camueller/WeatherStation-Wunderground-GSM/fritzing/WetterstationDaidalos_bb.png

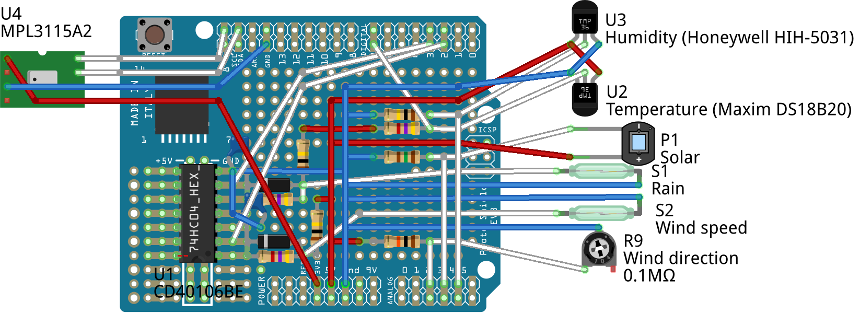
fritzing/WetterstationDaidalos_bb.png
