camueller/WeatherStation-Wunderground-GSM/fritzing/WetterstationDaidalos_schem.png

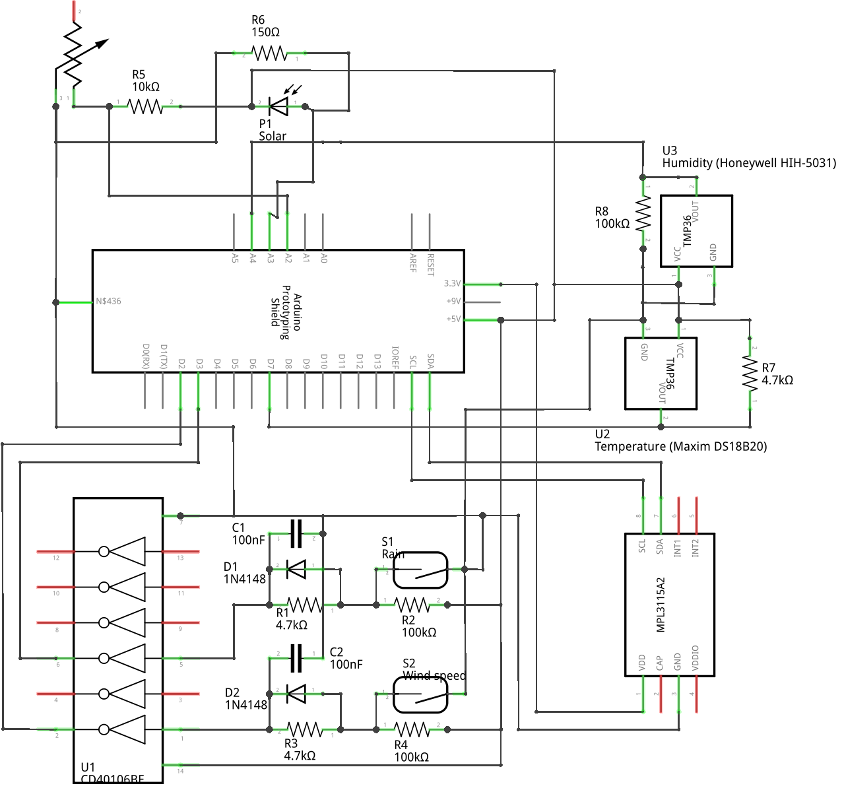
fritzing/WetterstationDaidalos_schem.png
