camueller/WeatherStation-Wunderground-GSM/pics/ArduinoUNO.JPG

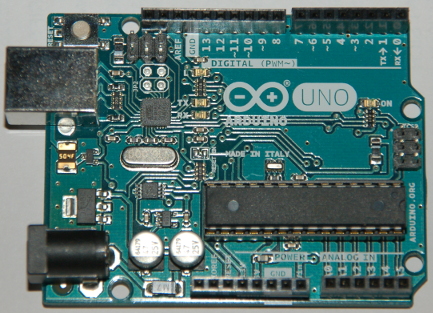
pics/ArduinoUNO.JPG
