camueller/WeatherStation-Wunderground-GSM/pics/Container.JPG

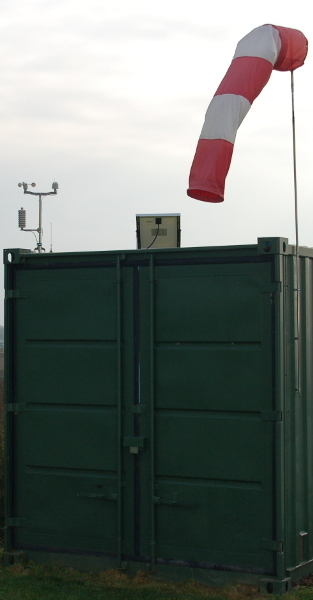
pics/Container.JPG
