camueller/WeatherStation-Wunderground-GSM/pics/EFCom.JPG

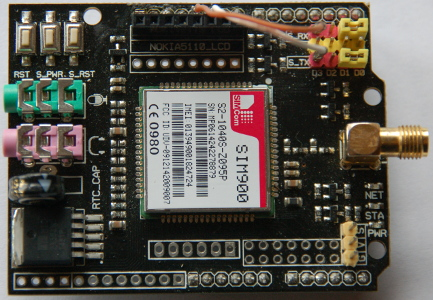
pics/EFCom.JPG
