camueller/WeatherStation-Wunderground-GSM/pics/ProtoShield.JPG

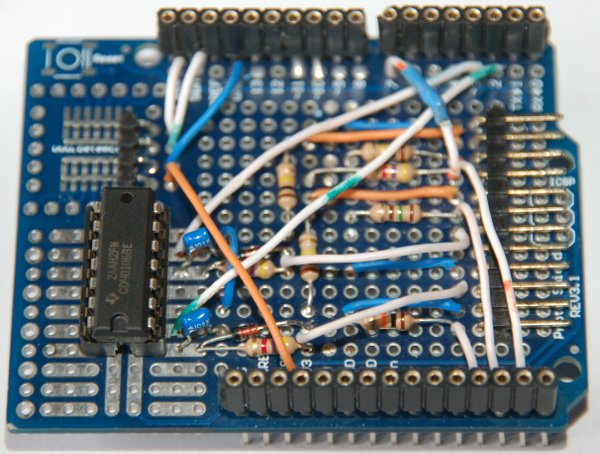
pics/ProtoShield.JPG
