camueller/WeatherStation-Wunderground-GSM/pics/Pyranometer2.JPG

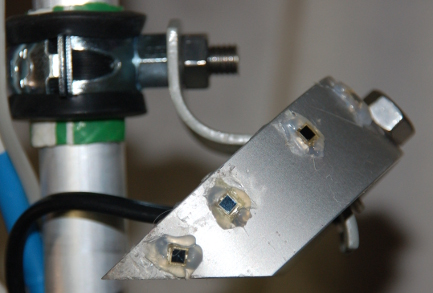
pics/Pyranometer2.JPG
