camueller/WeatherStation-Wunderground-GSM/pics/ShieldStack2.JPG

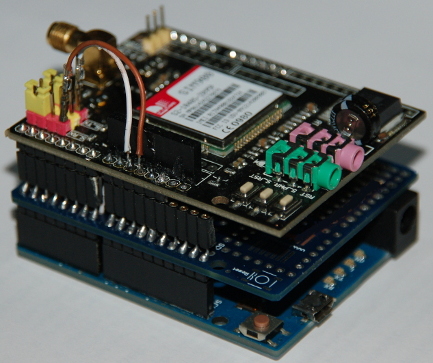
pics/ShieldStack2.JPG
