camueller/WeatherStation-Wunderground-GSM/pics/ShieldStack.JPG

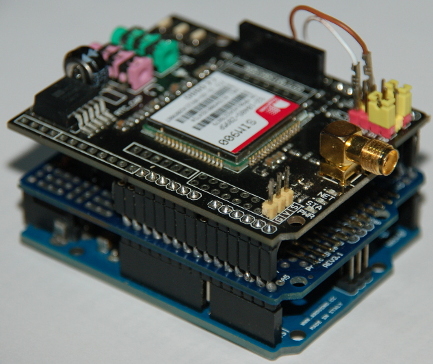
pics/ShieldStack.JPG
