camueller/WeatherStation-Wunderground-GSM/pics/SolarBausatz.png

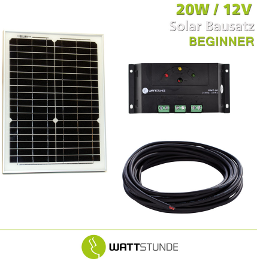
pics/SolarBausatz.png
