camueller/WeatherStation-Wunderground-GSM/pics/sonnenstand_mit_sensoren.gif

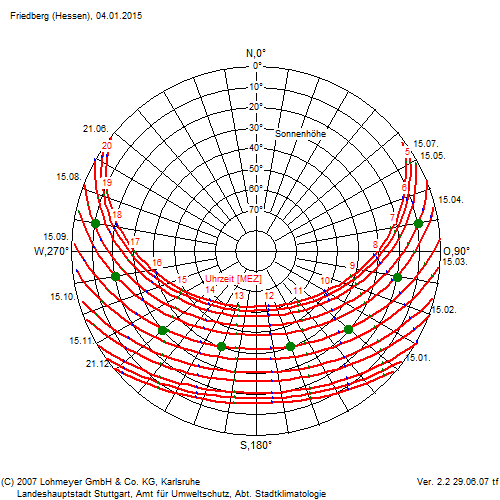
pics/sonnenstand_mit_sensoren.gif
