camueller/WeatherStation-Wunderground-GSM/pics/StevensonScreen.JPG

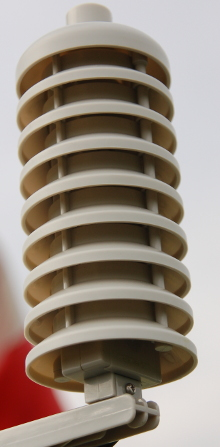
pics/StevensonScreen.JPG
