camueller/WeatherStation-Wunderground-GSM/pics/StevensonScreenGehaeuseGeschlossen.JPG

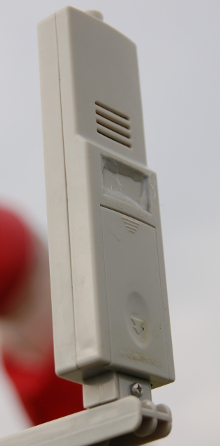
pics/StevensonScreenGehaeuseGeschlossen.JPG
