camueller/WeatherStation-Wunderground-GSM/pics/StevensonScreenPlatine.JPG

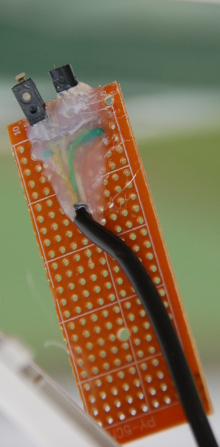
pics/StevensonScreenPlatine.JPG
