camueller/WeatherStation-Wunderground-GSM/pics/StiftBuchsenleiste.JPG

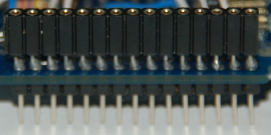
pics/StiftBuchsenleiste.JPG
