camueller/WeatherStation-Wunderground-GSM/pics/Stromstaerke.png

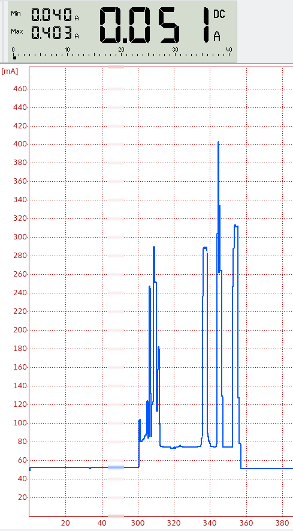
pics/Stromstaerke.png
