camueller/WeatherStation-Wunderground-GSM/pics/Wetterstation-widget.png

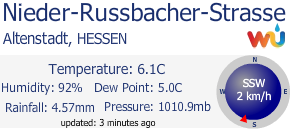
pics/Wetterstation-widget.png
