camueller/WeatherStation-Wunderground-GSM/pics/WetterstationMitSchaltschrank.JPG

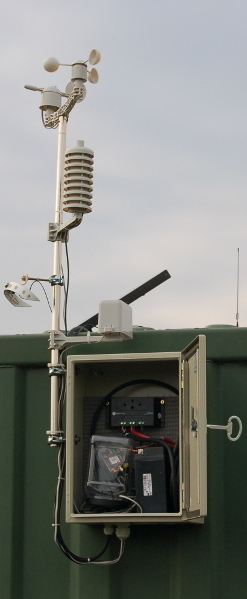
pics/WetterstationMitSchaltschrank.JPG
