camueller/WeatherStation-Wunderground-GSM/pics/WH1080Ausseneinheit.png

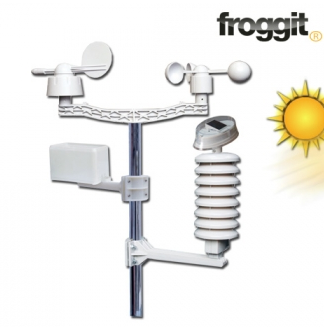
pics/WH1080Ausseneinheit.png
