camueller/WeatherStation-Wunderground-GSM/pics/WindmesserKugellagerAlt.JPG

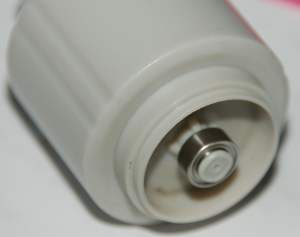
pics/WindmesserKugellagerAlt.JPG
