camueller/WeatherStation-Wunderground-GSM/pics/WindmesserKugellagerNeu.JPG

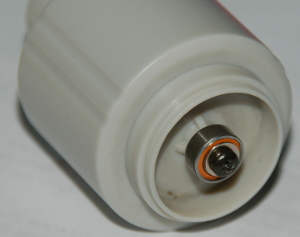
pics/WindmesserKugellagerNeu.JPG
