camueller/WeatherStation-Wunderground-GSM/arduino/Humidity.ino

/*
 This Arduino sketch controls a personal weather station and uses a GSM shield to upload data to wunderground.com.
 For updates check https://github.com/camueller/WeatherStation-Wunderground-GSM
 */

//////////////
// Variables
//////////////

//////////////
// Set up
//////////////

void setupHumidity() {
}

//////////////
// Loop
//////////////

void loopHumidity() {
  int value = analogReadSmoothed(humidityPin);
#ifdef DEBUG_WS  
    Serial.print(F("humidity (0-1023)="));
    Serial.println(value);
#endif
  // from data sheet
  humidity = ((value/1023.0-0.1515)/0.00636)/(1.0546-0.00216*temperature);
  if(humidity > 100) {
    humidity = 100;
  }
  dewpoint = dewPointFast(temperature, humidity);
  
#ifdef INFO_WS
  Serial.print(F("Humidity="));
  Serial.print(humidity, 1);
  Serial.print(F("%, Dewpoint="));
  Serial.print(dewpoint, 1);
  Serial.println(F("*C"));
#endif  
}

// delta max = 0.6544 wrt dewPoint()
// 5x faster than dewPoint()
// reference: http://en.wikipedia.org/wiki/Dew_point
double dewPointFast(double celsius, double humidity) {
  double a = 17.271;
  double b = 237.7;
  double temp = (a * celsius) / (b + celsius) + log(humidity/100);
  double Td = (b * temp) / (a - temp);
  return Td;
}
