camueller/WeatherStation-Wunderground-GSM/arduino/SolarRadiation.ino

/*
 This Arduino sketch controls a personal weather station and uses a GSM shield to upload data to wunderground.com.
 For updates check https://github.com/camueller/WeatherStation-Wunderground-GSM
 */
 
//////////////
// Variables
//////////////


//////////////
// Set up
//////////////

void setupSolarRadiation() {
}

//////////////
// Loop
//////////////

void loopSolarRadiation() {
  int solarRadiationRead = analogReadSmoothed(solarRadiationPin);
  solarRadiation = map(solarRadiationRead);
  
#ifdef INFO_WS
  Serial.print(F("Solar radiation="));
  Serial.println(solarRadiation);
#endif
}

int map(int value)  { 
  // Correlation to other stations reporting solar radiation
  //
  //          IHESSENA6   IHESSENS5
  //          analogRead  W/m2
  //          150 Ohm
  // 28.07.14             880
  // 07.02.14 422         358
  //
  return value;
}
